rbalreira/pap/components/Pressure Button.PNG

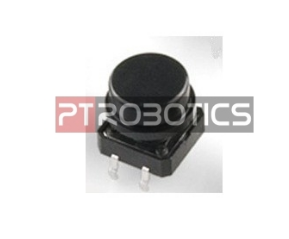
components/Pressure Button.PNG
