rbalreira/pap/components/relay.JPG

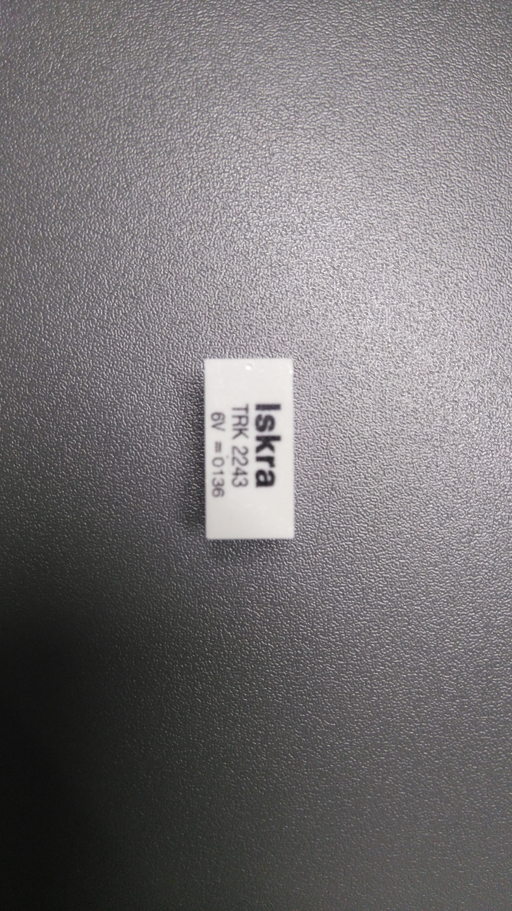
components/relay.JPG
