rbalreira/pap/components/RF decoder.PNG

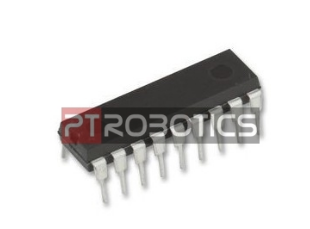
components/RF decoder.PNG
