rbalreira/pap/components/RF encoder.PNG

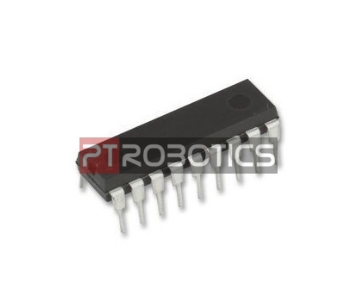
components/RF encoder.PNG
