rbalreira/pap/components/RF receiver.PNG

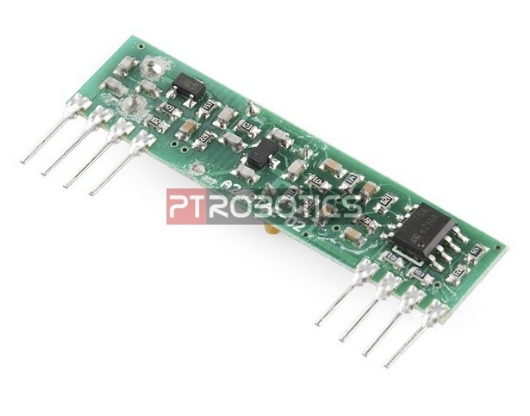
components/RF receiver.PNG
