rbalreira/pap/components/ULN2803_used.jpg

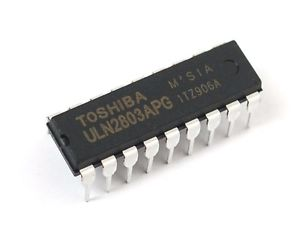
components/ULN2803_used.jpg
