rbalreira/pap/components/Vibrating motor.PNG

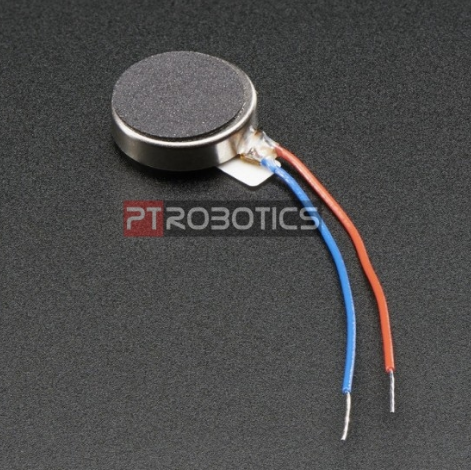
components/Vibrating motor.PNG
