rbalreira/pap/assembly_pictures/circuit.JPG

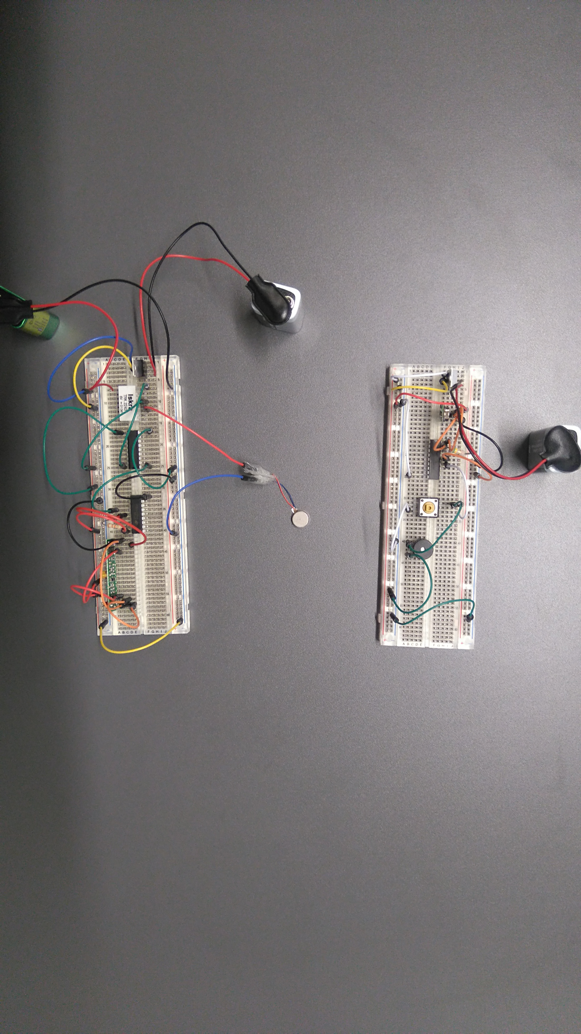
assembly_pictures/circuit.JPG
