rbalreira/pap/assembly_pictures/circuit_2.JPG

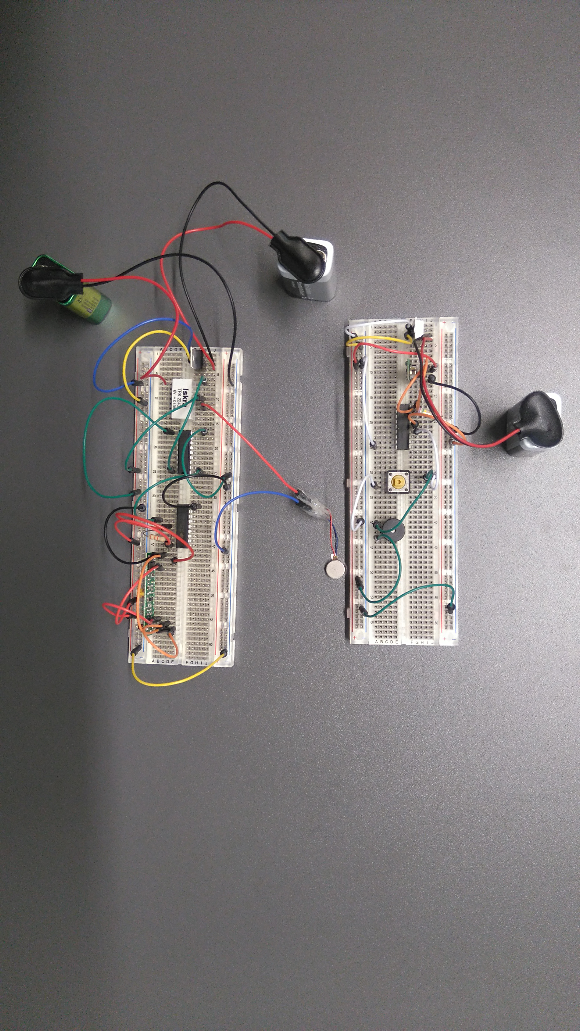
assembly_pictures/circuit_2.JPG
