rbalreira/pap/assembly_pictures/circuit_6.JPG

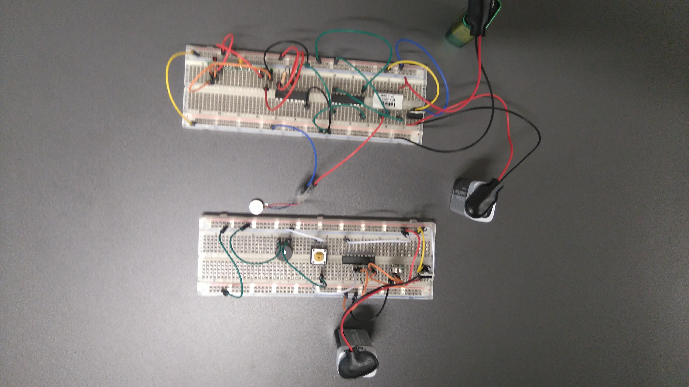
assembly_pictures/circuit_6.JPG
