rbalreira/pap/assembly_pictures/receiver.JPG

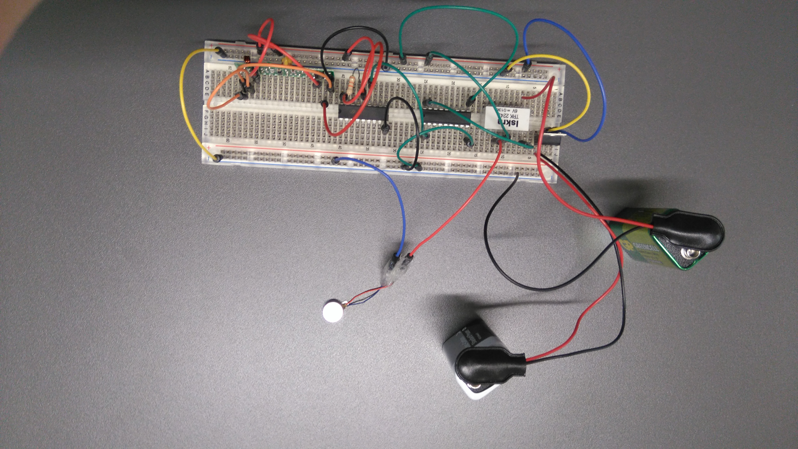
assembly_pictures/receiver.JPG
