rbalreira/pap/assembly_pictures/receiver_3.JPG

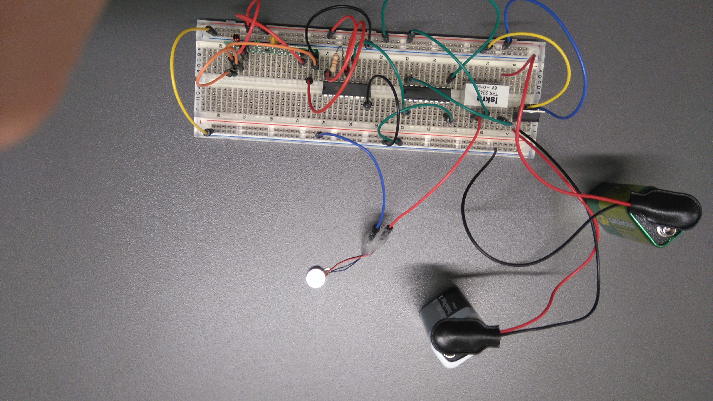
assembly_pictures/receiver_3.JPG
