rbalreira/pap/assembly_pictures/receiver_4.JPG

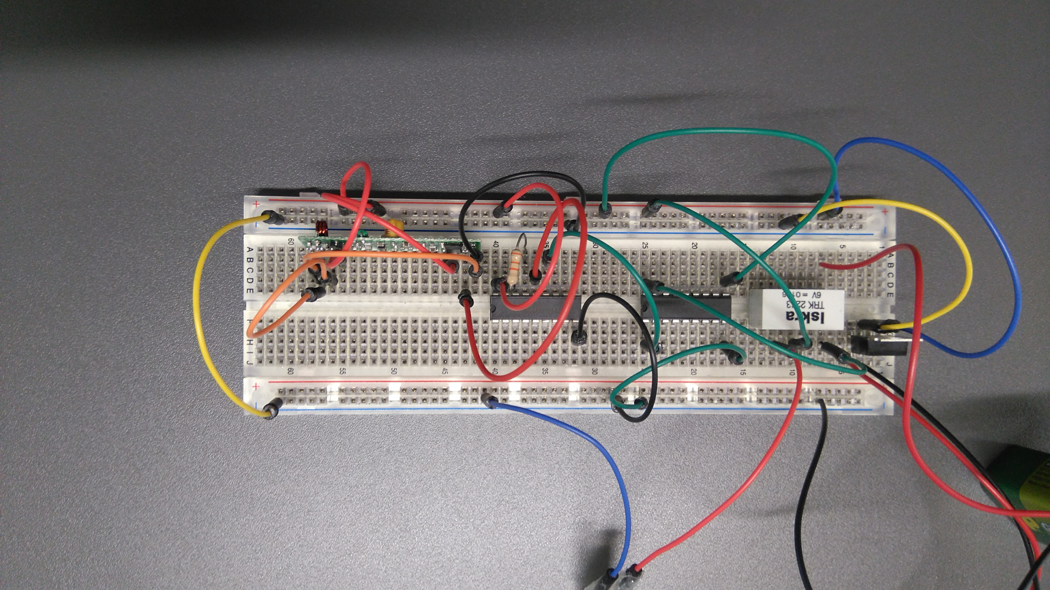
assembly_pictures/receiver_4.JPG
