rbalreira/pap/assembly_pictures/receiver_5.JPG

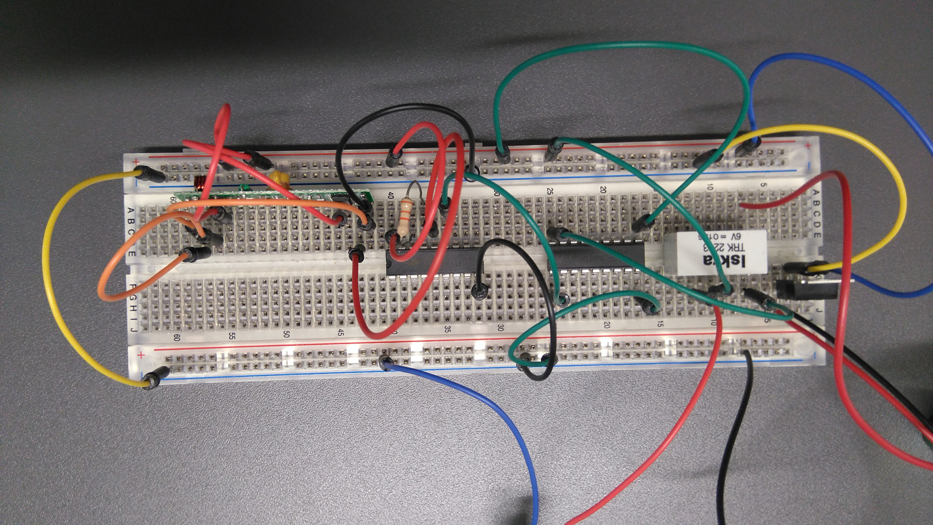
assembly_pictures/receiver_5.JPG
