rbalreira/pap/assembly_pictures/receiver_6.JPG

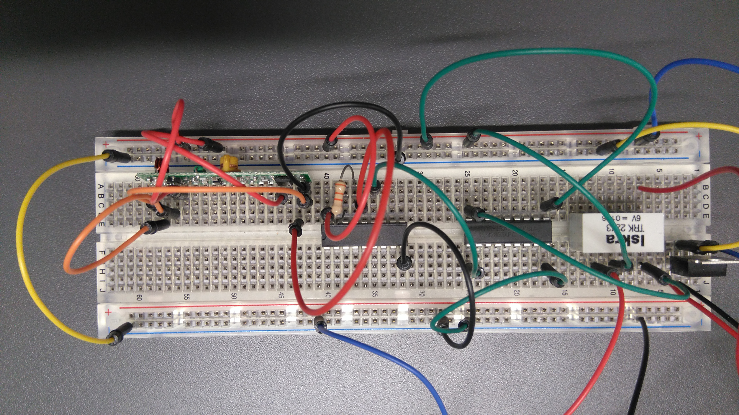
assembly_pictures/receiver_6.JPG
