rbalreira/pap/assembly_pictures/receiver_7.JPG

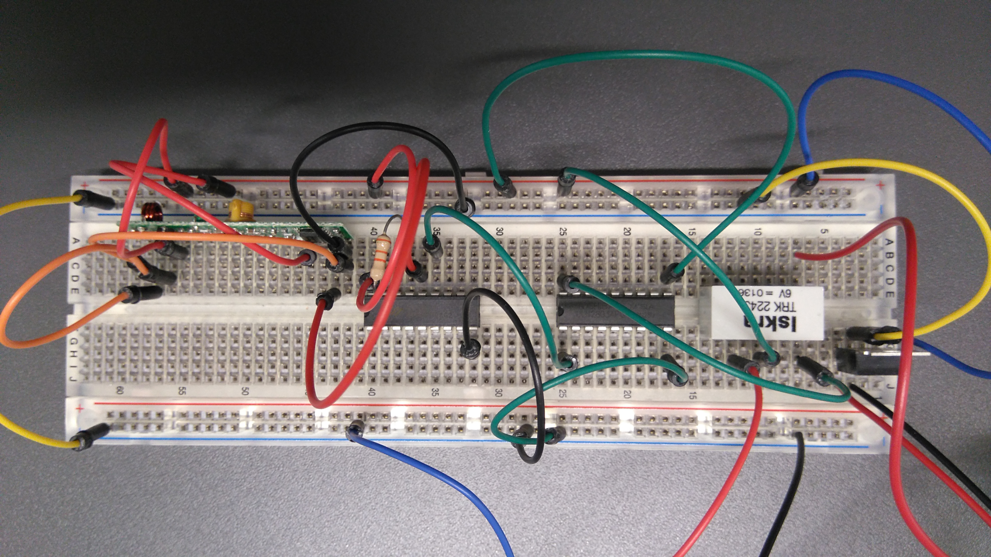
assembly_pictures/receiver_7.JPG
