rbalreira/pap/assembly_pictures/receiver_8.JPG

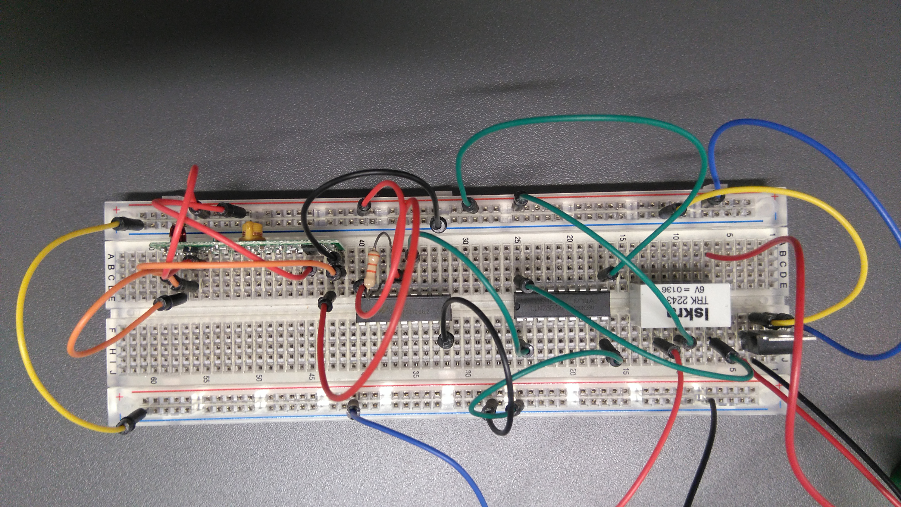
assembly_pictures/receiver_8.JPG
