rbalreira/pap/assembly_pictures/receiver_9.JPG

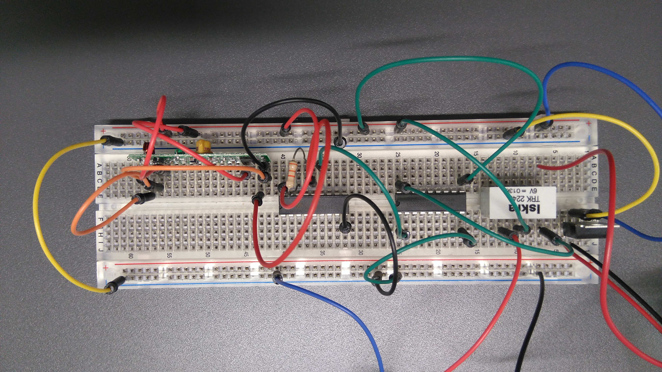
assembly_pictures/receiver_9.JPG
