rbalreira/pap/assembly_pictures/receiver_10.JPG

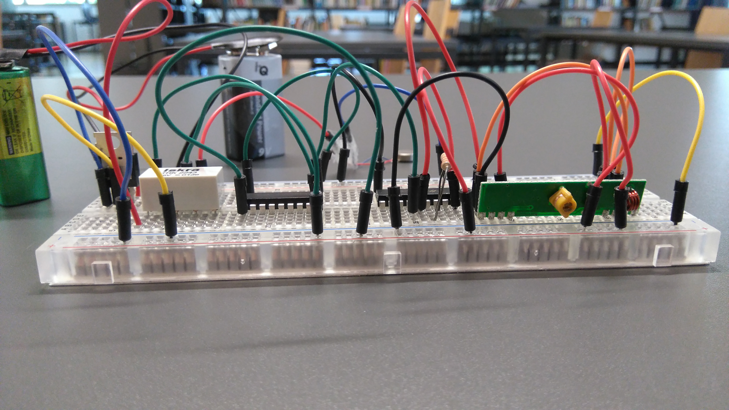
assembly_pictures/receiver_10.JPG
