rbalreira/pap/assembly_pictures/receiver_11.JPG

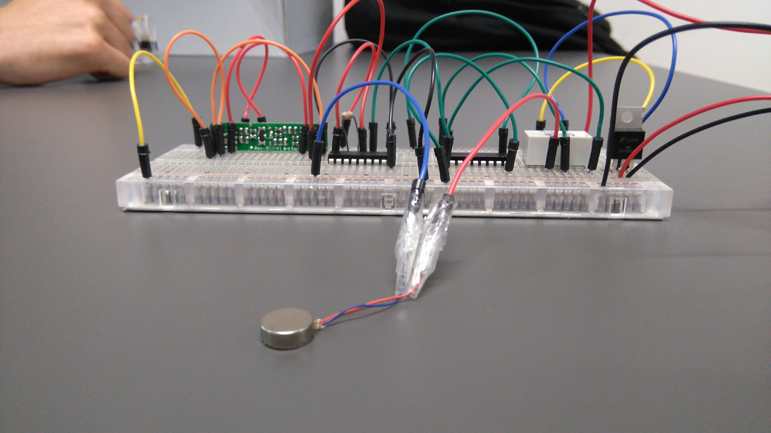
assembly_pictures/receiver_11.JPG
