rbalreira/pap/assembly_pictures/receiver_12.JPG

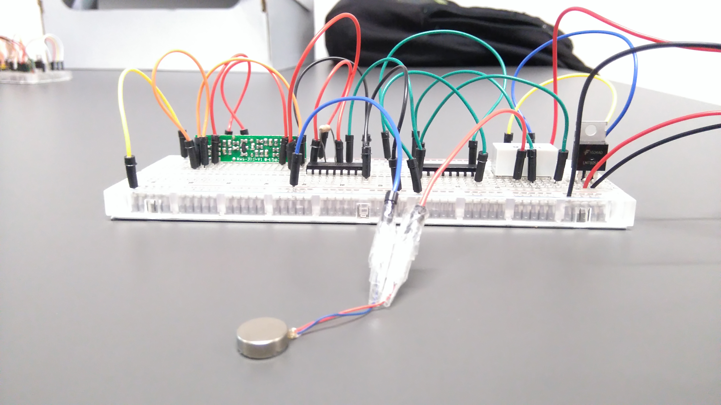
assembly_pictures/receiver_12.JPG
