rbalreira/pap/assembly_pictures/receiver_13.JPG

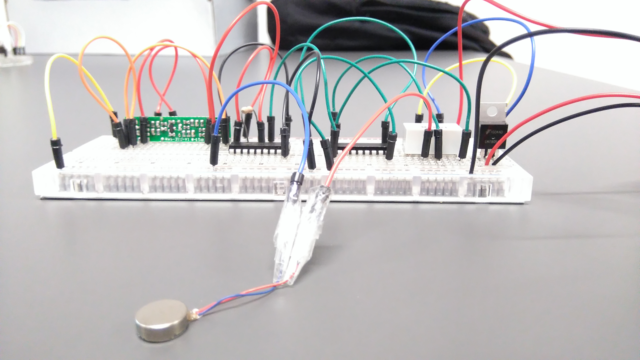
assembly_pictures/receiver_13.JPG
