rbalreira/pap/assembly_pictures/receiver_15.JPG

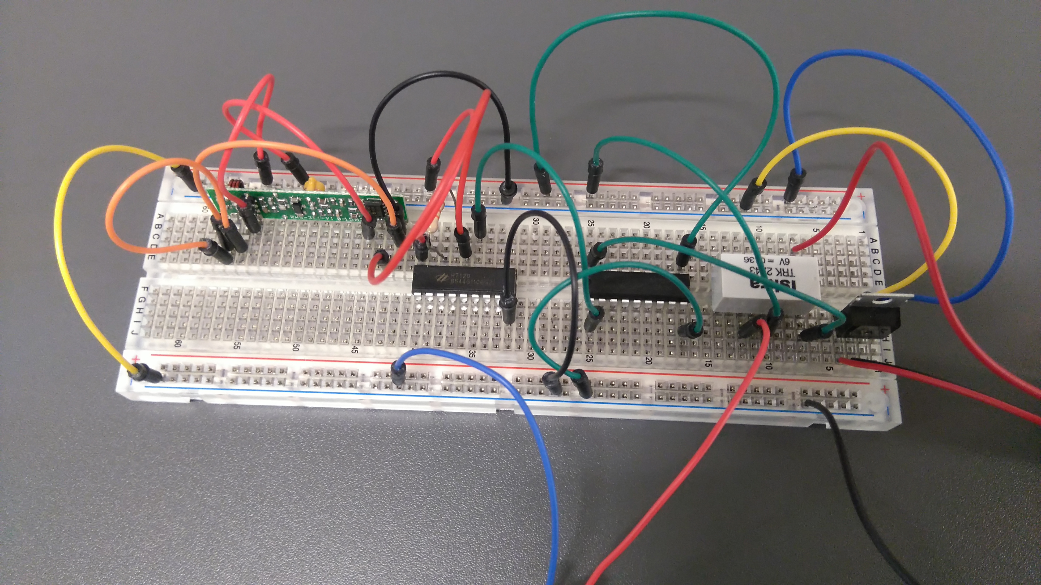
assembly_pictures/receiver_15.JPG
