rbalreira/pap/assembly_pictures/receiver_16.JPG

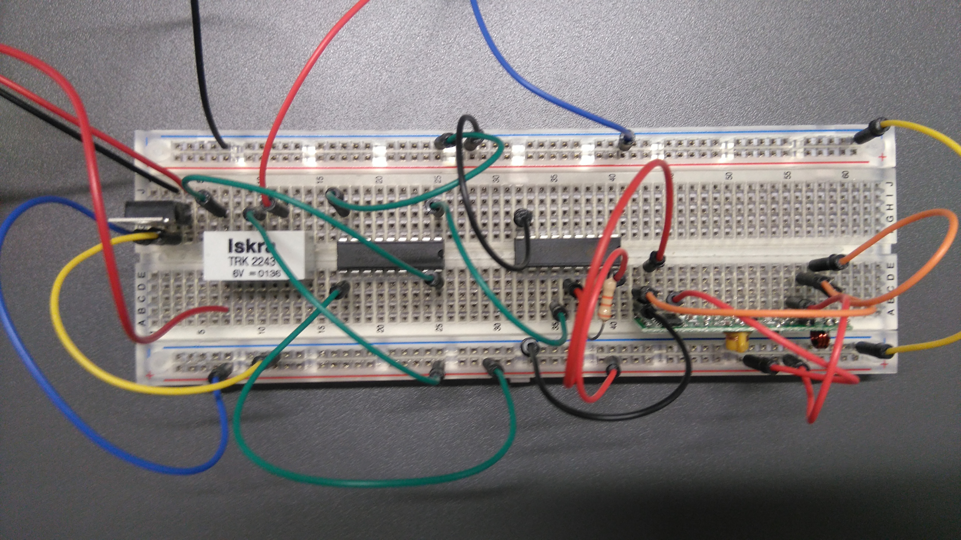
assembly_pictures/receiver_16.JPG
