rbalreira/pap/assembly_pictures/receiver_17.JPG

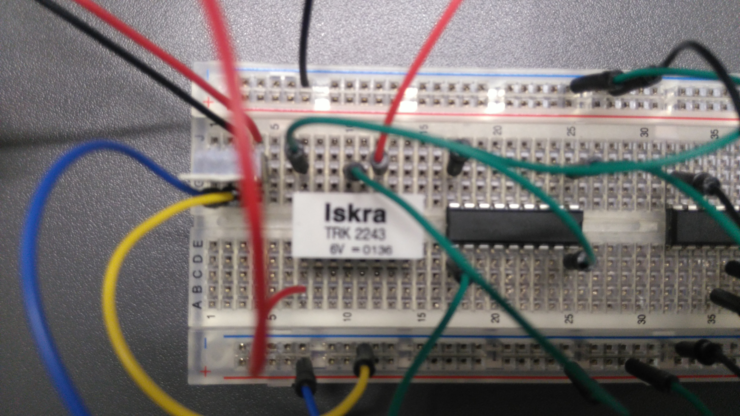
assembly_pictures/receiver_17.JPG
