rbalreira/pap/assembly_pictures/receiver_18.JPG

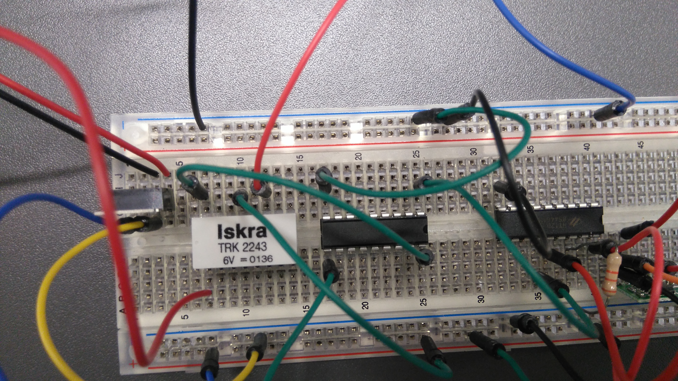
assembly_pictures/receiver_18.JPG
