rbalreira/pap/assembly_pictures/receiver_19.JPG

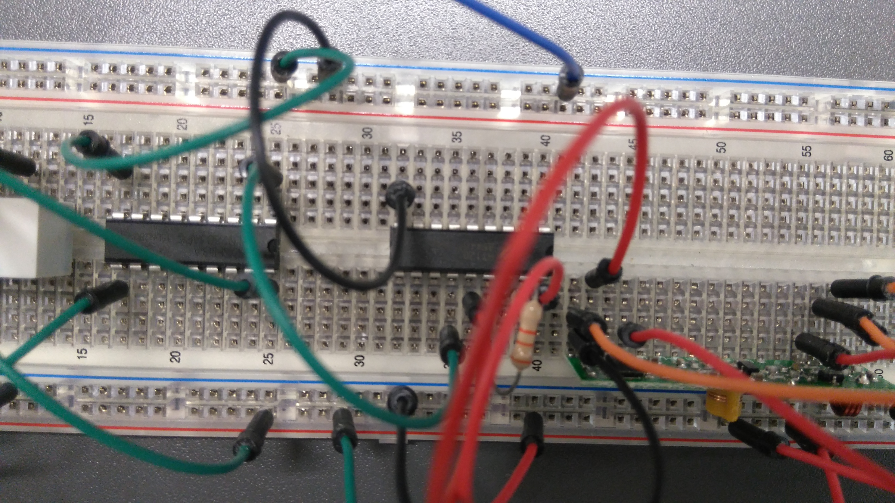
assembly_pictures/receiver_19.JPG
