rbalreira/pap/assembly_pictures/receiver_20.JPG

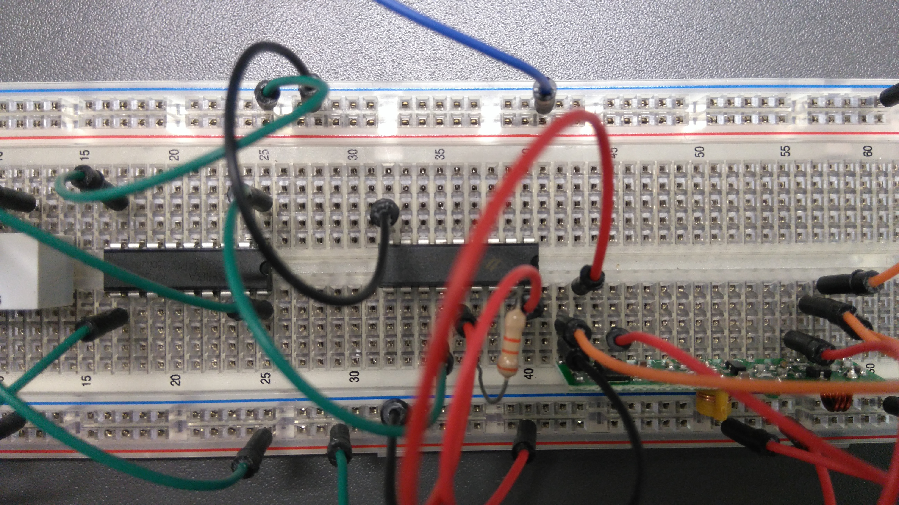
assembly_pictures/receiver_20.JPG
