rbalreira/pap/assembly_pictures/receiver_21.JPG

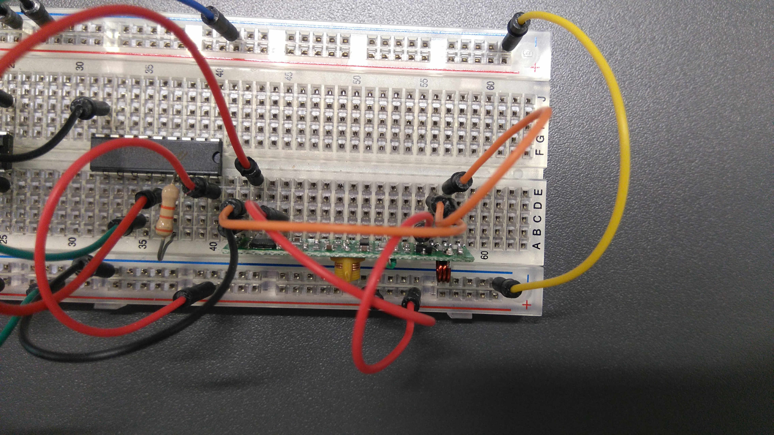
assembly_pictures/receiver_21.JPG
