rbalreira/pap/assembly_pictures/receiver_22.JPG

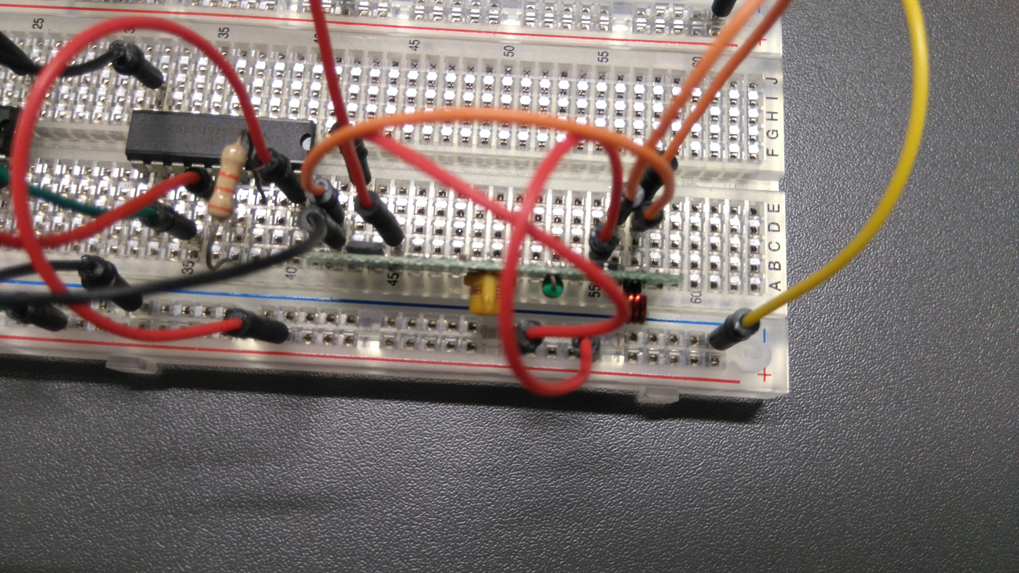
assembly_pictures/receiver_22.JPG
