rbalreira/pap/assembly_pictures/receiver_23.JPG

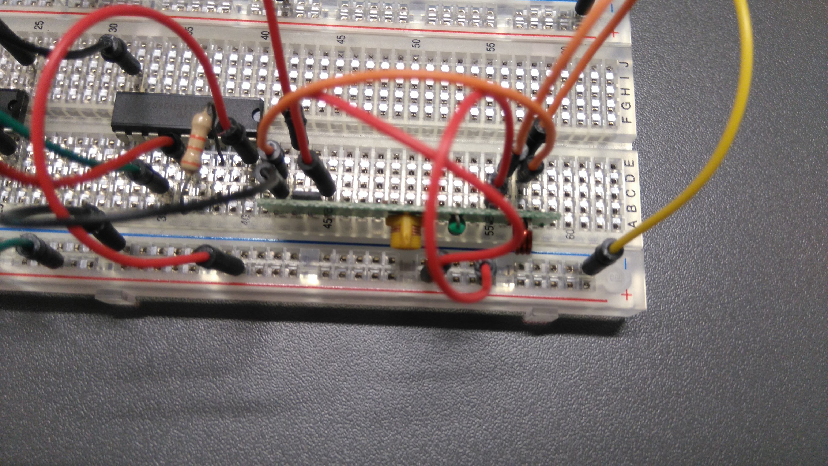
assembly_pictures/receiver_23.JPG
