rbalreira/pap/assembly_pictures/receiver_24.JPG

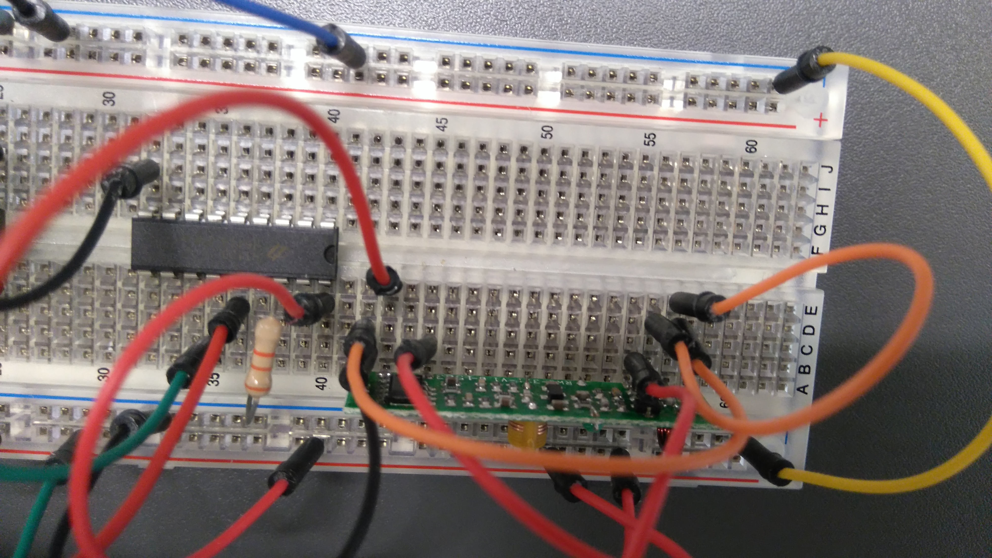
assembly_pictures/receiver_24.JPG
