rbalreira/pap/assembly_pictures/receiver_25.JPG

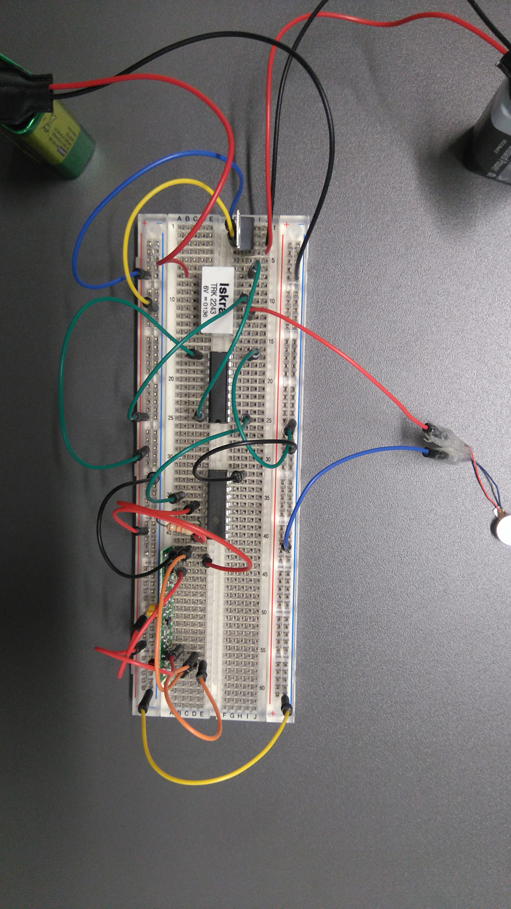
assembly_pictures/receiver_25.JPG
