rbalreira/pap/assembly_pictures/schema/receiver_schema.jpg

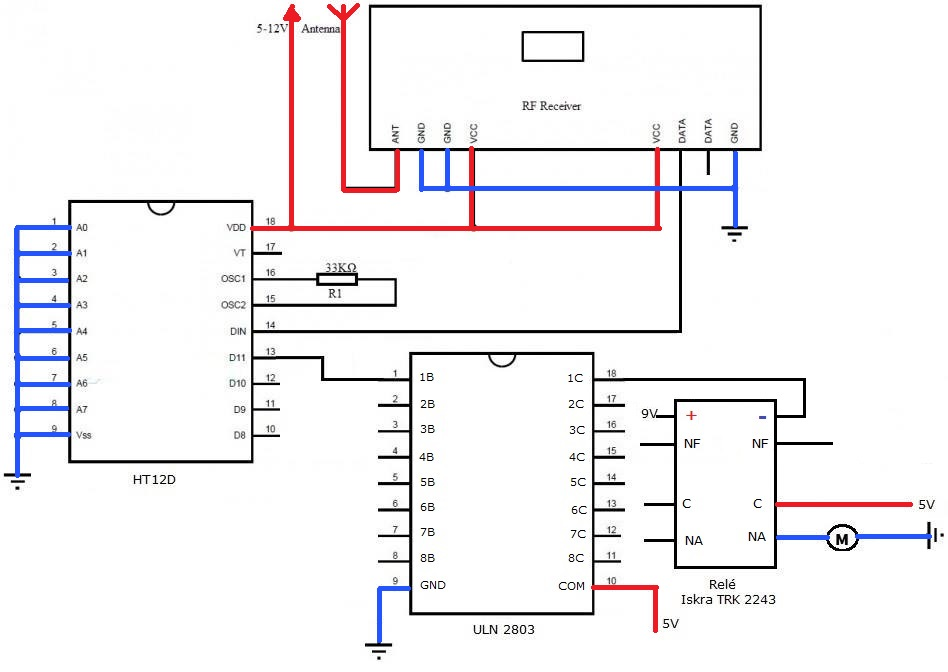
assembly_pictures/schema/receiver_schema.jpg
