rbalreira/pap/assembly_pictures/schema/rf_receiver_pins.PNG

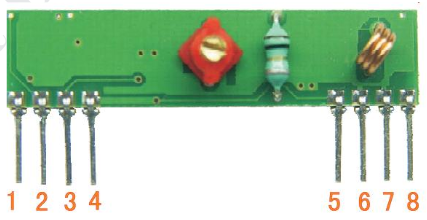
assembly_pictures/schema/rf_receiver_pins.PNG
