rbalreira/pap/assembly_pictures/schema/rf_transmitter.PNG

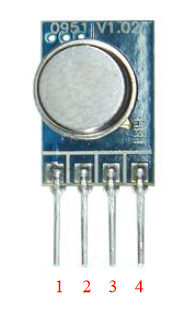
assembly_pictures/schema/rf_transmitter.PNG
