rbalreira/pap/assembly_pictures/schema/schema_circuit.PNG

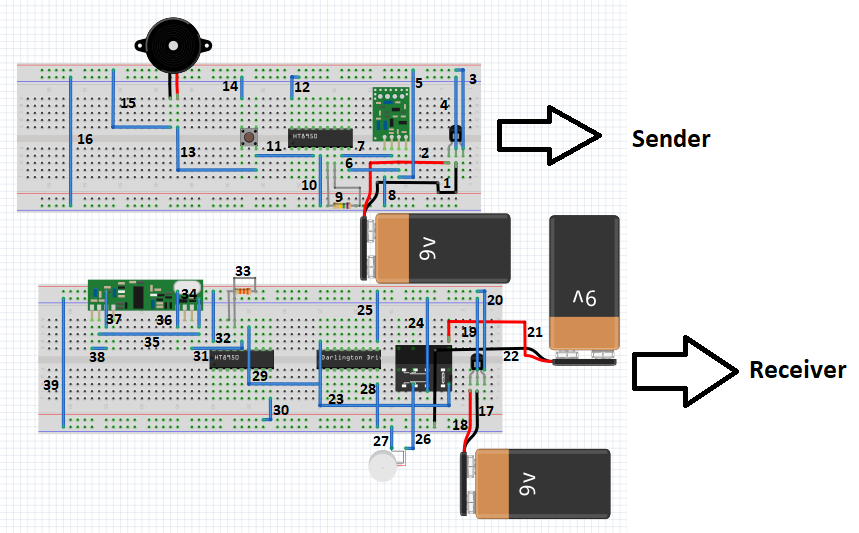
assembly_pictures/schema/schema_circuit.PNG
