rbalreira/pap/assembly_pictures/sender.JPG

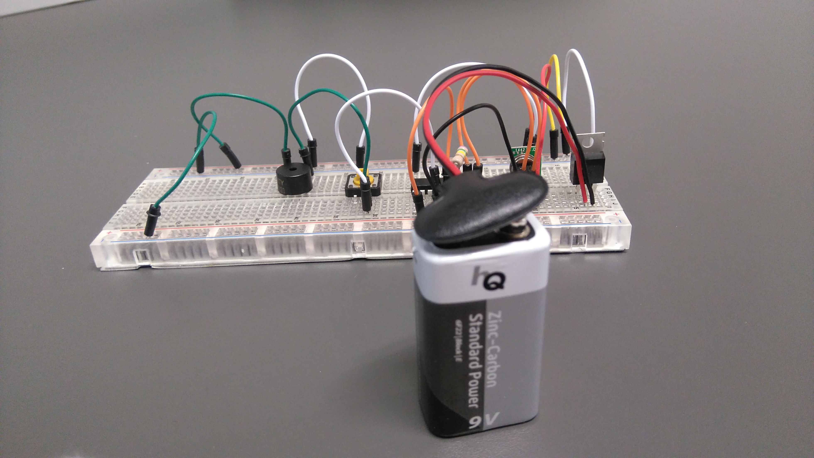
assembly_pictures/sender.JPG
