rbalreira/pap/assembly_pictures/sender_2.JPG

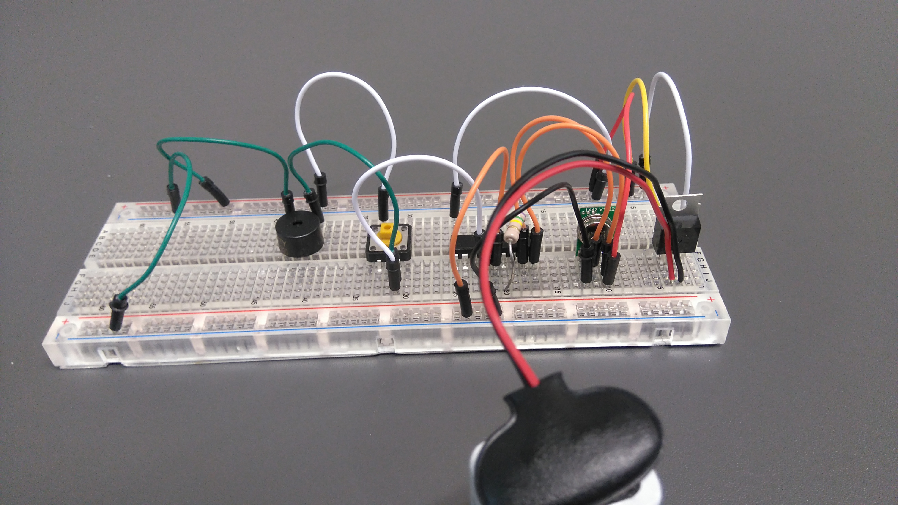
assembly_pictures/sender_2.JPG
