rbalreira/pap/assembly_pictures/sender_3.JPG

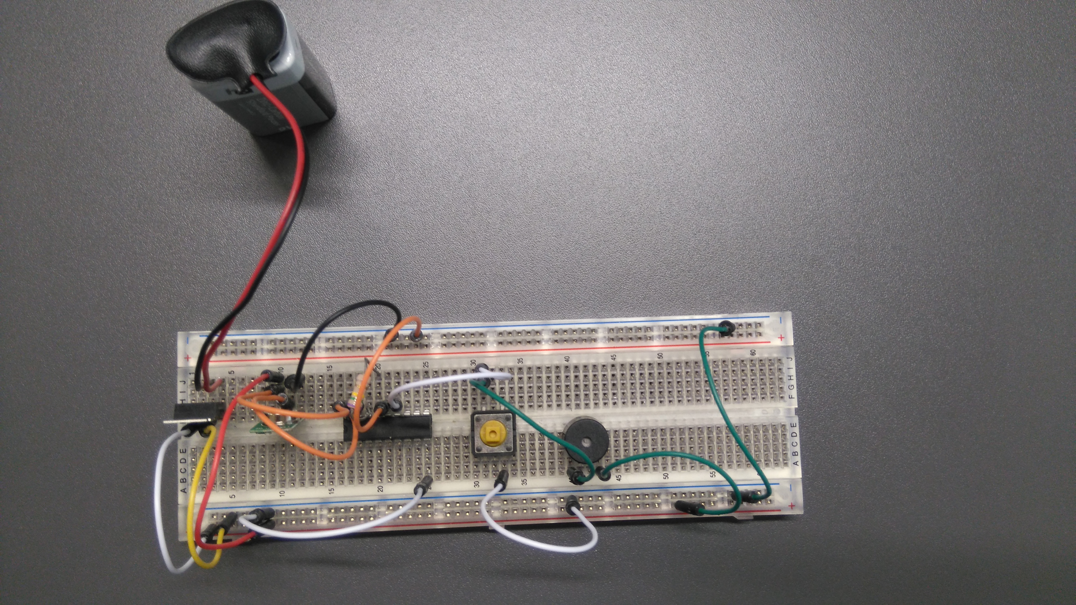
assembly_pictures/sender_3.JPG
