rbalreira/pap/assembly_pictures/sender_4.JPG

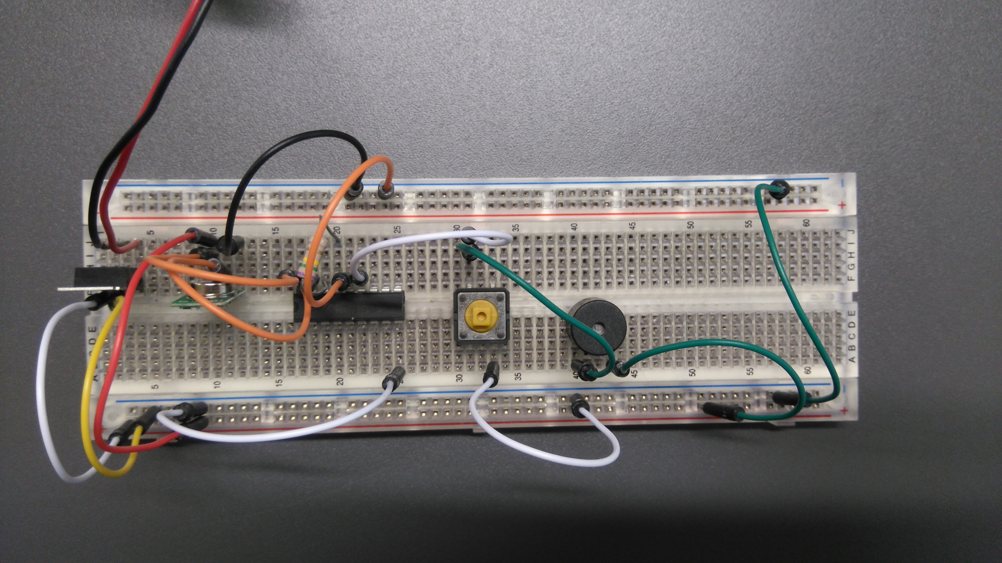
assembly_pictures/sender_4.JPG
