rbalreira/pap/assembly_pictures/sender_5.JPG

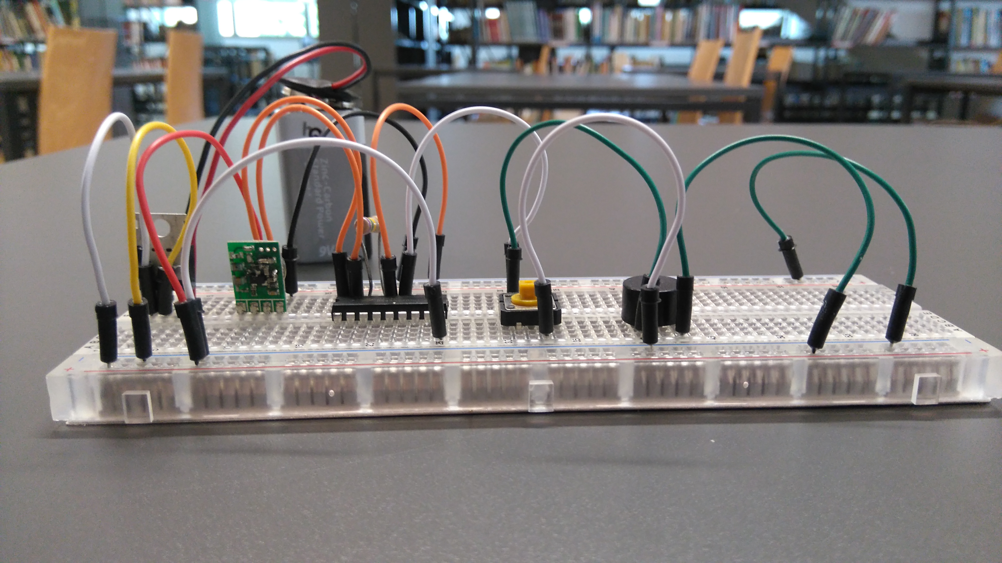
assembly_pictures/sender_5.JPG
