rbalreira/pap/assembly_pictures/sender_6.JPG

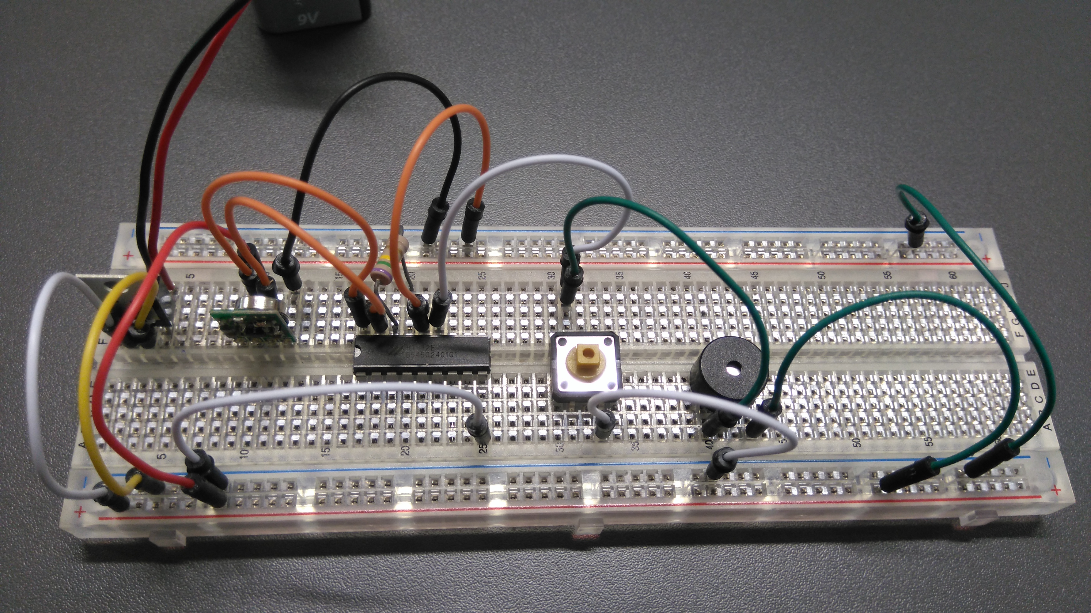
assembly_pictures/sender_6.JPG
