rbalreira/pap/assembly_pictures/sender_7.JPG

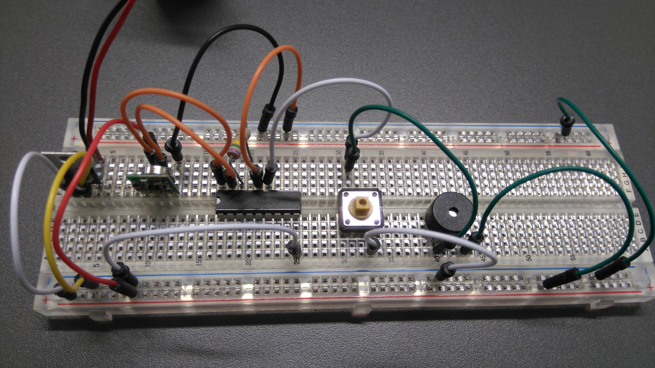
assembly_pictures/sender_7.JPG
