rbalreira/pap/assembly_pictures/sender_8.JPG

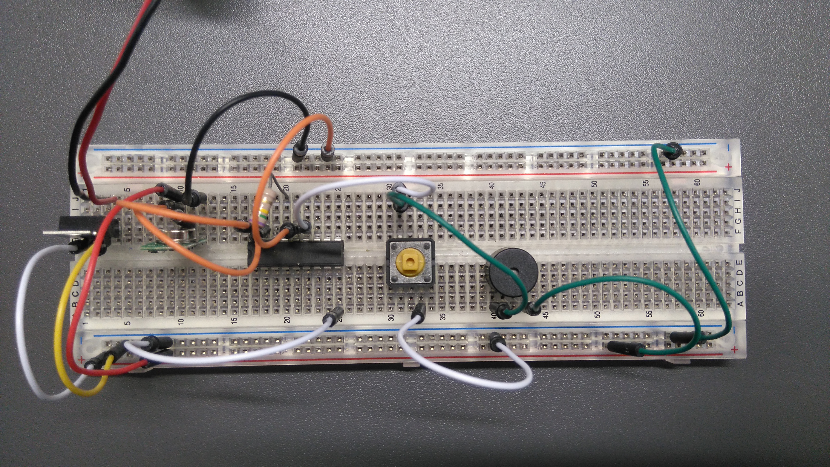
assembly_pictures/sender_8.JPG
