rbalreira/pap/assembly_pictures/sender_9.JPG

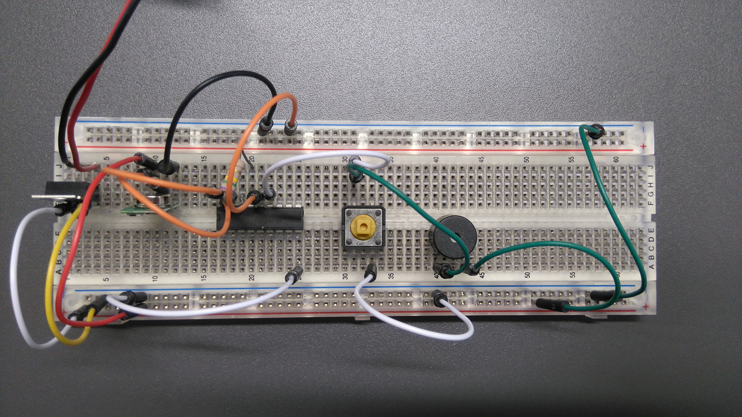
assembly_pictures/sender_9.JPG
