rbalreira/pap/assembly_pictures/sender_10.JPG

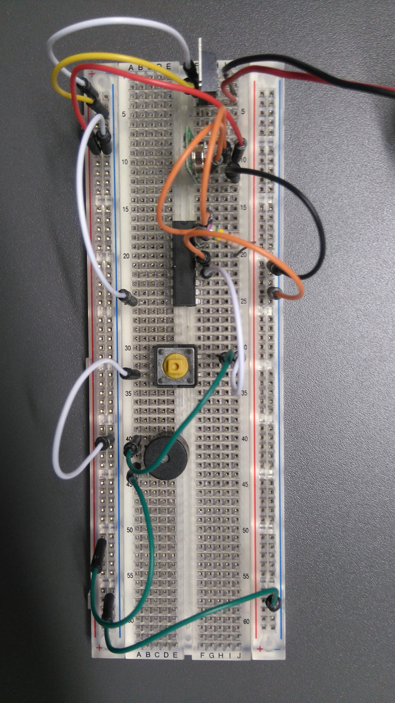
assembly_pictures/sender_10.JPG
